eg321/esp32-motorized-roller-blinds/src/Helpers/ButtonsHelper.h

#ifndef ESP32_MOTORIZED_ROLLER_BLINDS_BUTTONSHELPER_H
#define ESP32_MOTORIZED_ROLLER_BLINDS_BUTTONSHELPER_H

#define BUTTONS_CLIENT_ID 200

#include "Button2.h"

class ButtonsHelper {
public:
    Button2 buttonUp, buttonDown;
    bool useButtons;
    uint8_t pinButtonUp;
    uint8_t pinButtonDown;

    void setupButtons();

    void processButtons();
};


#endif //ESP32_MOTORIZED_ROLLER_BLINDS_BUTTONSHELPER_H
